duplico/booper.badge.lgbt/ccs_workspace/booper.badge.lgbt/rfm75.c

/// Low-level driver for HopeRF RFM75 module.
/**
 **
 **
 ** \file rfm75.c
 ** \author George Louthan
 ** \date   2023
 ** \copyright (c) 2018-2023 George Louthan @duplico. MIT License.
 */

#include <string.h>
#include <stdint.h>

#include <driverlib.h>

#include "badge.h"
#include "rfm75.h"

// Handy generic pin twiddling:
#define CSN_LOW_START RFM75_CSN_OUT &= ~RFM75_CSN_PIN
#define CSN_HIGH_END  RFM75_CSN_OUT |= RFM75_CSN_PIN

#define CE_ACTIVATE RFM75_CE_OUT |= RFM75_CE_PIN
#define CE_DEACTIVATE RFM75_CE_OUT &= ~RFM75_CE_PIN

// Local vars and buffers:
/// Persistent unicast address, to return pipe 0 to after ACKs.
uint16_t rfm75_unicast_addr = 0;

uint8_t payload[RFM75_PAYLOAD_SIZE] = {0};  ///< Buffer to hold TX/RX payload.

/// The RFM75 state tracks its progress through a sort of state machine.
uint8_t rfm75_state = RFM75_BOOT;

/// When this is 1, the application needs to call rfm75_deferred_interrupt().
volatile uint8_t f_rfm75_interrupt = 0;

/// Function pointer to the callback for a message RX.
rfm75_rx_callback_fn* rfm75_rx_done_cb;
/// Function pointer to the callback for a successful TX or a failed ACK.
rfm75_tx_callback_fn* rfm75_tx_done_cb;

/// The size of bank0_init_data in its first dimension.
#define BANK0_INITS 19

/// Initialization values in (addr,value) format for RFM75 register bank 0.
const uint8_t bank0_init_data[BANK0_INITS][2] = {
        { CONFIG, 0b011111101 }, //
        { 0x01, BIT0+BIT1 }, // Auto-ack for pipe0 (unicast)
        { 0x02, BIT0+BIT1 }, //Enable RX pipe 0 and 1
        { 0x03, 0b00000001 }, //RX/TX address field width 3byte
        { 0x04, 0b00000100 }, //auto-RT
        { 0x05, 0x10 }, //channel: 2400 + LS 7 of this field
        { 0x06, 0b00000111 }, //air data rate-1M,out power max, LNA gain high.
        { 0x07, 0b01110000 }, // Clear interrupt flags
        { 0x08, 0x00 }, // OBSERVE_TX - magic
        { 0x09, 0x00 }, // CD register - MAGIC
        // 0x0a - RX_ADDR_P0 - 3 bytes
        // 0x0b - RX_ADDR_P1 - 3 bytes
        // 0x10 - TX_ADDR - 5 bytes
        { 0x11, RFM75_PAYLOAD_SIZE }, //Number of bytes in RX payload in pipe0
        { 0x12, RFM75_PAYLOAD_SIZE }, //Number of bytes in RX payload in pipe1
        { 0x13, 0 }, //Number of bytes in RX payload in data pipe2 - disable
        { 0x14, 0 }, //Number of bytes in RX payload in data pipe3 - disable
        { 0x15, 0 }, //Number of bytes in RX payload in data pipe4 - disable
        { 0x16, 0 }, //Number of bytes in RX payload in data pipe5 - disable
        { 0x17, 0 },
        { 0x1c, 0x00 }, // No dynamic packet length
        { 0x1d, 0b00000001 } // 00000 | DPL | ACK_PAYLOAD | DYN_ACK
};

/// Receive a single byte of data from the RFM75.
uint8_t rfm75spi_recv_sync(uint8_t data) {
    while (!(RFM75_UCxIFG & UCTXIFG));
    RFM75_UCxTXBUF = data;
    while (!(RFM75_UCxIFG & UCRXIFG));
    return RFM75_UCxRXBUF;
}

/// Send a single byte of data to the RFM75.
void rfm75spi_send_sync(uint8_t data) {
    rfm75spi_recv_sync(data);
}

/// Read the RFM75 status register and return it.
uint8_t rfm75_get_status() {
    uint8_t recv;
    CSN_LOW_START;
    recv = rfm75spi_recv_sync(NOP_NOP);
    CSN_HIGH_END;
    return recv;
}

/// Issue the RFM75 a command with a single byte of data.
uint8_t send_rfm75_cmd(uint8_t cmd, uint8_t data) {
    uint8_t ret;
    CSN_LOW_START;
    rfm75spi_send_sync(cmd);
    ret = rfm75spi_recv_sync(data);
    CSN_HIGH_END;
    return ret;
}

/// Issue the RFM75 a command `cmd` with `data_len` bytes of `data`.
void send_rfm75_cmd_buf(uint8_t cmd, uint8_t *data, uint8_t data_len) {
    CSN_LOW_START;
    // We write everything in REVERSE ORDER!
    rfm75spi_send_sync(cmd);
    for (uint8_t i=1; i<=data_len; i++) {
        rfm75spi_send_sync(data[data_len-i]);
    }
    CSN_HIGH_END;
}

/// Issue the RFM75 a command and read the response into a buffer.
void read_rfm75_cmd_buf(uint8_t cmd, uint8_t *data, uint8_t data_len) {
    CSN_LOW_START;
    rfm75spi_send_sync(cmd);
    for (uint8_t i=1; i<=data_len; i++) {
        data[data_len-i] = rfm75spi_recv_sync(0xab);
    }
    CSN_HIGH_END;
}

/// Read a single byte from a register from the active bank.
uint8_t rfm75_read_reg(uint8_t cmd) {
    cmd &= 0b00011111;
    CSN_LOW_START;
    rfm75spi_send_sync(cmd);
    uint8_t recv = rfm75spi_recv_sync(0xff);
    CSN_HIGH_END;
    return recv;
}

/// Write a single byte to a register in the active bank.
void rfm75_write_reg(uint8_t reg, uint8_t data) {
    reg &= 0b00011111;
    send_rfm75_cmd(WRITE_REG | reg, data);
}

/// Write multiple bytes of data to a register
void rfm75_write_reg_buf(uint8_t reg, uint8_t *data, uint8_t data_len) {
    reg &= 0b00011111;
    send_rfm75_cmd_buf(WRITE_REG | reg, data, data_len);
}

/// Set the RFM75's active register bank.
void rfm75_select_bank(uint8_t bank) {
    volatile uint8_t currbank = rfm75_get_status() & 0x80;
    if ((currbank && (bank==0)) || ((currbank==0) && bank)) {
        send_rfm75_cmd(ACTIVATE_CMD, 0x53);
    }
}

/// Set the current unicast address (PRX pipe 0).
void set_unicast_addr(uint16_t addr) {
    uint8_t rx_addr_p0[3] = {UNICAST_LSB, 100, 0};
    rx_addr_p0[0] = UNICAST_LSB;
    rx_addr_p0[1] = addr & 0xff;
    rx_addr_p0[2] = (addr & 0xff00) >> 8; // MSB
    rfm75_write_reg_buf(RX_ADDR_P0, rx_addr_p0, 3);
}

/// Configure the RFM75 for Primary Receive mode.
void rfm75_enter_prx() {
    rfm75_state = RFM75_RX_INIT;
    CE_DEACTIVATE;
    // Power up & enter PRX (Primary RX)
    set_unicast_addr(rfm75_unicast_addr);
    rfm75_write_reg(CONFIG, CONFIG_MASK_TX_DS +
                    CONFIG_MASK_MAX_RT + CONFIG_EN_CRC +
                    CONFIG_CRCO_2BYTE + CONFIG_PWR_UP +
                    CONFIG_PRIM_RX);

    // Clear interrupts: STATUS=BIT4|BIT5|BIT6
    rfm75_write_reg(STATUS, BIT4|BIT5|BIT6);

    CSN_LOW_START;
    rfm75spi_send_sync(FLUSH_TX);
    CSN_HIGH_END;

    // Enter RX mode.
    CE_ACTIVATE;

    // This takes 130 us, but that doesn't matter because we'll be in
    //  STANDBY in the meantime.

    rfm75_state = RFM75_RX_LISTEN;
}

/// Query whether a call to rfm75_tx() is allowed right now.
uint8_t rfm75_tx_avail() {
    return rfm75_state == RFM75_RX_LISTEN || rfm75_state == RFM75_TX_DONE ||
           rfm75_state == RFM75_RX_READY;
}

/// Transmit an RFM75 message to a given address, or RFM75_BROADCAST_ADDR.
/**
 ** \param addr  The destination address, or RFM75_BROADCAST_ADDR.
 ** \param noack Disable acknowledgments. This is only valid when
 **                  `addr` is a unicast destination, because broadcast
 **                  messages can't be acknowledged anyway.
 ** \param data  A pointer to the buffer containing the data to transmit.
 ** \param len   The length of the data buffer.
 **
 ** Note that it's important for `len` to be the same as RFM75_PAYLOAD_SIZE,
 ** or else strange things may happen.
 **
 ** This function may be called any time `rfm75_tx_avail()` returns a true
 ** value, which includes any time during either the `rfm75_rx_done_cb()` or
 ** `rfm75_tx_done_cb()` callbacks.
 **
 */
void rfm75_tx(uint16_t addr, uint8_t noack, uint8_t* data, uint8_t len) {
    if (!rfm75_tx_avail()) {
        return;
    }

    CE_DEACTIVATE;

    CSN_LOW_START;
    rfm75spi_send_sync(FLUSH_RX);
    CSN_HIGH_END;

    rfm75_state = RFM75_TX_INIT;
    uint8_t wr_cmd = WR_TX_PLOAD_NOACK;


    rfm75_write_reg(CONFIG, CONFIG_MASK_RX_DR +
                            CONFIG_EN_CRC + CONFIG_CRCO_2BYTE +
                            CONFIG_PWR_UP + CONFIG_PRIM_TX);

    CSN_LOW_START;
    rfm75spi_send_sync(FLUSH_TX);
    CSN_HIGH_END;

    // Setup our destination address:
    uint8_t tx_addr[3] = {0};

    if (addr == RFM75_BROADCAST_ADDR) {
        // broadcast!
        tx_addr[0] = BROADCAST_LSB;
    } else {
        // unicast!
        // Since we're going to listen for ACKs, we need to change our P0 ADDR
        //  to be the same as the destination address.
        set_unicast_addr(addr);
        tx_addr[0] = UNICAST_LSB;
        if (!noack) {
            wr_cmd = WR_TX_PLOAD; // request an ACK.
        }
    }

    tx_addr[1] = addr & 0xff;
    tx_addr[2] = (addr & 0xff00) >> 8; // MSB

    rfm75_write_reg_buf(TX_ADDR, tx_addr, 3);

    // Clear interrupts: STATUS=BIT4|BIT5|BIT6
    rfm75_write_reg(STATUS, BIT4|BIT5|BIT6);

    rfm75_state = RFM75_TX_FIFO;
    // Write the payload:
    send_rfm75_cmd_buf(wr_cmd, data, len);
    rfm75_state = RFM75_TX_SEND;
    CE_ACTIVATE;
    // Now we wait for an IRQ to let us know it's sent.
}

/// Handle RFM75 IRQ, posting to the registered RX and TX callbacks as needed.
/**
 * This function needs to be called every time that the RFM75 IRQ is asserted,
 * preferably as soon as possible. However, for performance reasons it's
 * important that this not be called from inside the interrupt service routine
 * itself. The ISR sets a flag called `f_rfm75_interrupt`, which signals to the
 * main program that this function needs to be called. While this deferred
 * interrupt is pending, the radio will have limited to no background
 * functionality (depending on whether we are in PTX or PRX mode).
 *
 * This function will, as needed, clear the interrupt vector on the RFM75,
 * and clear the interrupt flag that was set in this driver's ISR.
 *
 * This function will also invoke `rfm75_tx_done_cb()` or `rfm75_rx_done_cb()`
 * as appropriate.
 *
 *
 */
void rfm75_deferred_interrupt() {
    f_rfm75_interrupt = 0;
    // Get the interrupt vector from the RFM75 module:
    uint8_t iv = rfm75_get_status();

    if (iv & BIT4) { // no ACK interrupt
        // Clear the interrupt flag on the radio module:
        rfm75_state = RFM75_TX_DONE;
    }

    if (iv & BIT5 && rfm75_state == RFM75_TX_SEND) { // TX interrupt
        // The ISR already took us back to standby.
        // Clear the interrupt flag on the radio module:
        rfm75_state = RFM75_TX_DONE;
    }

    // Determine whether we need to send a TX callback, which covers
    //  all the cases of (a) we sent a non-ackable message,
    //  (b) we sent an ackable message that was acked, and
    //  (c) we sent an ackable message that was NOT acked.
    if (iv & (BIT4|BIT5)) { // TX or NOACK.
        rfm75_write_reg(STATUS, BIT5|BIT4|BIT6);
        // We pass TRUE if we did NOT receive a NOACK flag from
        //  the radio module (meaning EITHER, it was ACKed, OR
        //  we did not request an ACK).
        rfm75_tx_done_cb(!(iv & BIT4));

        // It's important that our tx_done callback function is able to call
        //  `rfm75_tx()`. All the cleanup we needed to do to re-TX has already
        //  been done. So we need to check if we're still in `RFM75_TX_DONE`
        //  after the callback returns. If we are, it's OK to return to PRX
        //  mode. If not, we're elsewhere in the TX state machine and should
        //  leave `rfm75_state` alone.
        if (rfm75_state == RFM75_TX_DONE) {
            rfm75_enter_prx();
        }
    }

    if (iv & BIT6 && rfm75_state == RFM75_RX_LISTEN) { // RX interrupt
        // We've received something.
        rfm75_state = RFM75_RX_READY;

        // Read the FIFO. No need to flush it; it's deleted when read.
        read_rfm75_cmd_buf(RD_RX_PLOAD, payload, RFM75_PAYLOAD_SIZE);

        // Invoke the registered callback function.
        // 0b1110 masks the pipe ID out of the IV.
        rfm75_rx_done_cb(payload, RFM75_PAYLOAD_SIZE, (iv & 0b1110) >> 1);

        // After rfm75_rx_done_cb returns (and ONLY after it returns), the
        //  payload_in is stale and is allowed to be overwritten.

        if (rfm75_state == RFM75_RX_READY) {
            // The rfm75_rx_done_cb callback did NOT invoke a transmit:
            // So now we can tell the radio module that we're done with it:
            //  Clear the interrupt flag on the module...
            rfm75_write_reg(STATUS, BIT6);
            //  ... and assert CE, to listen more.
            CE_ACTIVATE;
            rfm75_state = RFM75_RX_LISTEN;
        } else {
            // rfm75_rx_done_cb has called rfm75_tx, so the following happened:
            //  1. rfm75_state is changed.
            //      That's fine, we don't care.
            //  2. CE_DEACTIVATE, then CE_ACTIVATE were called.
            //      That means we don't need to handle it.
            //  3. The CONFIG register was written.
            //      Ok, great, we're in the proper TX config.
            //  4. All interrupts are cleared
            //      Awesome. We're done here.
            //  No cleanup is necessary.
        }
    }
}

/// Perform a RFM75 self-test and return a 1 if it appears to be working.
/**
 ** This function MAY NOT be called prior to calling `rfm75_init()`.
 */
uint8_t rfm75_post() {
    // The MSB of the status register is the active bank, and ACTIVATE 0x53
    //  is supposed to change the active bank. Let's see if it works.
    volatile uint8_t bank_one = rfm75_get_status() & 0x80;
    send_rfm75_cmd(ACTIVATE_CMD, 0x53);
    volatile uint8_t bank_two = rfm75_get_status() & 0x80;

    rfm75_select_bank(0); // Go back to the normal bank.

    if (bank_one == bank_two) {
        return 0;
    }
    return 1;
}

/// Initialize the GPIO and peripheral pins required for the RFM75.
void rfm75_io_init() {
    CSN_HIGH_END; // initialize deselected.
    CE_DEACTIVATE; // initialize deactivated.

    // Setup USCI
    RFM75_UCxCTLW0 |= UCSWRST;
    RFM75_UCxBRW = 1; // Clock scaler: if SMCLK isn't 1 MHz this much change.
    // clear control word:
    RFM75_UCxCTLW0 &= ~(UCCKPH + UCCKPL + UC7BIT + UCMSB +
            UCMST + UCMODE_3 + UCSYNC + UCSSEL_3);
    // set control word:
    RFM75_UCxCTLW0 |=    UCSSEL__SMCLK + // use SMCLK
            UCMSB + //MSB first
            UCCKPH + // mode 01 or whatever
            UCMODE_0 + // 3-pin
            UCMST + // master mode
            UCSYNC; // synchronous mode.

    // and enable!
    RFM75_UCxCTLW0 &= ~UCSWRST;
}

/// Initialize the RFM75 module with its address and callback functions.
void rfm75_init(uint16_t unicast_address, rfm75_rx_callback_fn* rx_callback,
                rfm75_tx_callback_fn* tx_callback)
{
    //  one of the chinese documents (rfm73 -> rfm75 migration) says that it should be executed after every PWR_UP, not only during initialization

    // Disable the IRQ pin interrupt, while we set up our inputs.
    //  This may not be necessary, but is out of an abundance of caution
    //  because I suspect there may be certain circumstances under which
    //  undefined behavior may be possible if we're not certain that this
    //  is disabled ASAP in the initialization process.
    RFM75_IRQ_IE &= ~RFM75_IRQ_PIN;

    rfm75_io_init();

    rfm75_rx_done_cb = rx_callback;
    rfm75_tx_done_cb = tx_callback;

    // We're going totally synchronous on this; no interrupts at all.
    // We'll wait on the interrupt enables though, until after we've set up
    //  all of our register banks with the initial configuration

    rfm75_select_bank(1);

    // Some of these go MOST SIGNIFICANT BYTE FIRST: (so we start with 0xE2.)
    //  (we show them here LEAST SIGNIFICANT BYTE FIRST because we
    //   reverse everything we send.)
    // Basically, these are just stupid magic numbers that took a lot of
    //  work with the stupid data sheet to get right. If you change them,
    //  things will probably break mysteriously.
    uint8_t bank1_config_0x00[][4] = {
        {0xe2, 0x01, 0x4b, 0x40}, // reserved (prescribed)
        {0x00, 0x00, 0x4b, 0xc0}, // reserved (prescribed)
        {0x02, 0x8c, 0xfc, 0xd0}, // reserved (prescribed)
        {0x21, 0x39, 0x00, 0x99}, // reserved (prescribed)
        {0x1b, 0x82, 0x96, 0xf9}, // 1 Mbps, 4 dBm (max power)
        {0xa6, 0x0f, 0x06, 0x24}, // 1 Mbps
    };

    for (uint8_t i=0; i<6; i++) {
        rfm75_write_reg_buf(i, bank1_config_0x00[i], 4);
    }

    //6,7,8,9,A,B - give them zeroes:

    uint8_t zeroes[4] = {0,0,0,0};
    for (uint8_t i=0; i<6; i++) {
        rfm75_write_reg_buf(0x06 + i, zeroes, 4);
    }

    uint8_t bank1_config_0x0c[][4] = {
                                      {0x05, 0x73, 0x12, 0x00}, // 130 us mode (PLL settle time?)
                                      {0x00, 0x80, 0xb4, 0x36}, // reserved?
    };

    for (uint8_t i=0; i<2; i++) {
        rfm75_write_reg_buf(0x0c+i, bank1_config_0x0c[i], 4);
    }

    // Set the prescribed ramp curve:
    uint8_t bank1_config_0x0e[11] = {0xff, 0xff, 0xfe, 0xf7, 0xcf, 0x20, 0x81,
                                     0x04, 0x08, 0x20, 0x41};
    rfm75_write_reg_buf(0x0e, bank1_config_0x0e, 11);

    // Let's start with bank 0:
    rfm75_select_bank(0);

    // Because we want the option of using dynamic ACKs, and possibly dynamic
    //  packet lengths as well, we need to determine whether this radio has
    //  had its FEATURE register ACTIVATED (by sending the ACTIVATE command
    //  followed by 0x73.)
    // But since a restart of our code does not necessarily mean that the radio
    //  has been restarted by a power cycle, and because the ACTIVATE command
    //  is a toggle,
    uint8_t test_feature_reg = 0;
    test_feature_reg = rfm75_read_reg(FEATURE);
    rfm75_write_reg(FEATURE, test_feature_reg ^ 0b00000111); // try to flip bits
    if (rfm75_read_reg(FEATURE) == test_feature_reg) {
        // In spite of trying to flip these, bits, they stayed the same.
        // Therefore, it needs to be ACTIVATED.
        send_rfm75_cmd(ACTIVATE_CMD, 0x73);
    } else {
        // else we're already ACTIVATED.
        // no need to run any command.
        // (and the FEATURE register will be configured in the master bank0
        //  config for loop, so there's no need to try to undo our bit flips
        //  here.)
    }

    for(uint8_t i=0;i<BANK0_INITS;i++)
        rfm75_write_reg(bank0_init_data[i][0], bank0_init_data[i][1]);

    // Setup addresses:
    rfm75_unicast_addr = unicast_address;
    uint8_t rx_addr_p1[3] = {BROADCAST_LSB, 0xff, 0xff};
    rfm75_write_reg_buf(RX_ADDR_P1, rx_addr_p1, 3);

    // Now, do a stupid magic process.
    rfm75_select_bank(1);

    // Ok, we've configured everything but haven't powered up yet...
    // From some Chinese datasheet or instructions or something:
    //  4. RFM75 PowerUP after the first packet of data sent unsuccessful solution
    //  RFM75 from the POWER DOWN state to switch to POWER UP state, send the first packet is not successful, the reason
    //  Is the PLL is not locked, the solution is as follows:
    //  Before transmitting data normally, please follow the following procedure:
    //  Power up = 1
    rfm75_write_reg(CONFIG, CONFIG_MASK_TX_DS +
                    CONFIG_MASK_MAX_RT + CONFIG_EN_CRC +
                    CONFIG_CRCO_2BYTE + CONFIG_PWR_UP +
                    CONFIG_PRIM_RX);
    __delay_cycles(1000 * MCLK_FREQ_MHZ);
    __delay_cycles(1000 * MCLK_FREQ_MHZ);
    //  Operate the bank1 register, writing a 1 to bit 25 of register 04
    // uint8_t bank1_config_0x00[][4][4]
    uint8_t bank1_config_toggle[4] = {0};
    memcpy(bank1_config_toggle, bank1_config_0x00[4], 4);
    bank1_config_toggle[3] |= 0x06;
    rfm75_write_reg_buf(0x04, bank1_config_toggle, 4);

    //  Wait 20us
    __delay_cycles(20 * MCLK_FREQ_MHZ);
    //  Operate the bank1 register, writing a 0 to bit 25 of register 04
    rfm75_write_reg_buf(0x04, bank1_config_0x00[4], 4);
    //  Wait for 0.5ms.
    __delay_cycles(500 * MCLK_FREQ_MHZ);
    //  Then normal launch.

    // Go back to the normal bank (0):
    rfm75_select_bank(0);

    // Flush our FIFOs just in case:
    CSN_LOW_START;
    rfm75spi_send_sync(FLUSH_RX);
    CSN_HIGH_END;
    CSN_LOW_START;
    rfm75spi_send_sync(FLUSH_TX);
    CSN_HIGH_END;

    // Enable our interrupts:
    RFM75_IRQ_IES |= RFM75_IRQ_PIN;
    RFM75_IRQ_IFG &= ~RFM75_IRQ_PIN;
    RFM75_IRQ_IE |= RFM75_IRQ_PIN;

    // And we're off to see the wizard!
    rfm75_enter_prx();
}

///The RFM75's interrupt pin ISR, which sets `f_rfm75_interrupt` to 1.
#pragma vector=RFMISR_VECTOR
__interrupt
void RFM_ISR(void)
{
    if (RFMxIV != RFMxIV_PxIFGx) {
        return;
    }
    f_rfm75_interrupt = 1;
    if (rfm75_state != RFM75_RX_LISTEN) {
        CE_DEACTIVATE; // stop sending, or whatever.
        // If we're listening, we don't need to do this.
        //  But if we MIGHT be sending, then there's the possibility that
        //  we could do bad things to the transceiver by holding CE high
        //  for too long (I think?)
    }
    LPM4_EXIT; // We may not be THIS sleepy, but this'll wake us from anything.
}
