duplico/booper.badge.lgbt/ccs_workspace/booper.badge.lgbt/animations.h

/// Animation headers for 2023 booper.badge.lgbt.
/**
 **
 **
 ** \file animations.h
 ** \author George Louthan
 ** \date   2023
 ** \copyright (c) 2023 George Louthan @duplico. MIT License.
 */

#ifndef ANIMATIONS_H_
#define ANIMATIONS_H_

#define ANIMATION_COUNT 7

extern eye_anim_t *animations[];

extern eye_anim_t anim_shifty;
extern eye_anim_t anim_boop;
extern eye_anim_t anim_new_badge;
extern eye_anim_t anim_seen_badge;

#endif /* ANIMATIONS_H_ */
